gruvin/kicad-freakduino/images/kicad-freakduino-r132.png

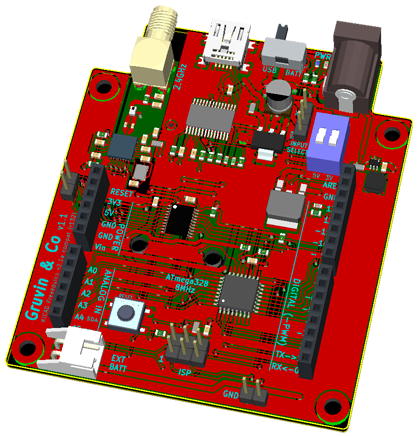
images/kicad-freakduino-r132.png
