gruvin/kicad-freakduino/images/pcb-3d-r69.png

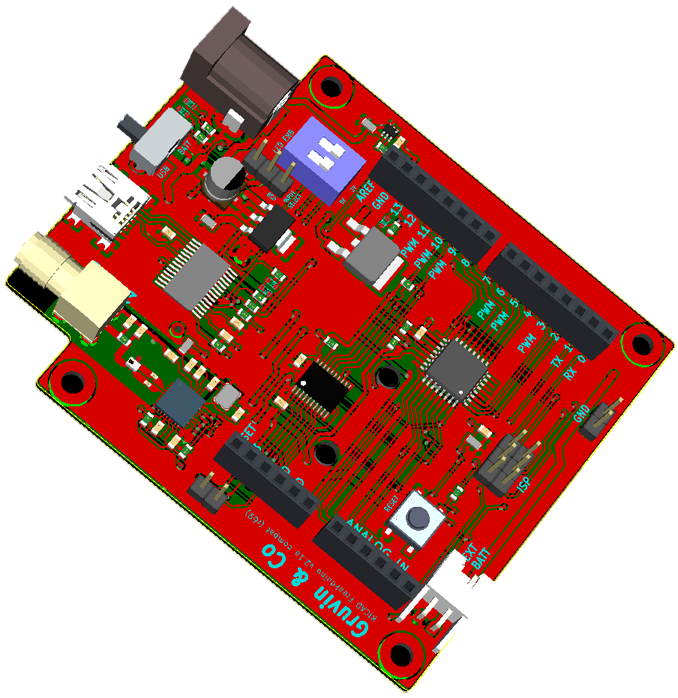
images/pcb-3d-r69.png
