gruvin/kicad-freakduino/images/pcb-3d-r168.png

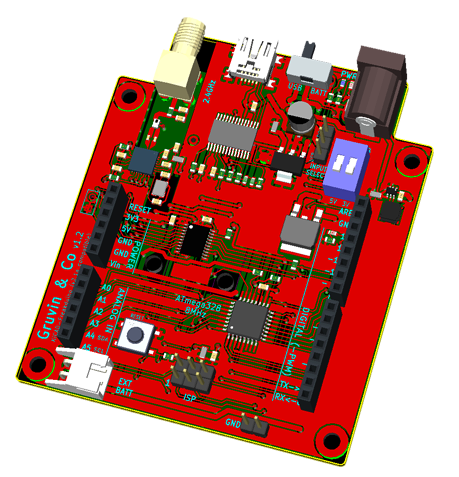
images/pcb-3d-r168.png
